nruth633/3-wheel-balancing-robot/firmware_main/Docs_Process/Acrylic_base_drawing.png

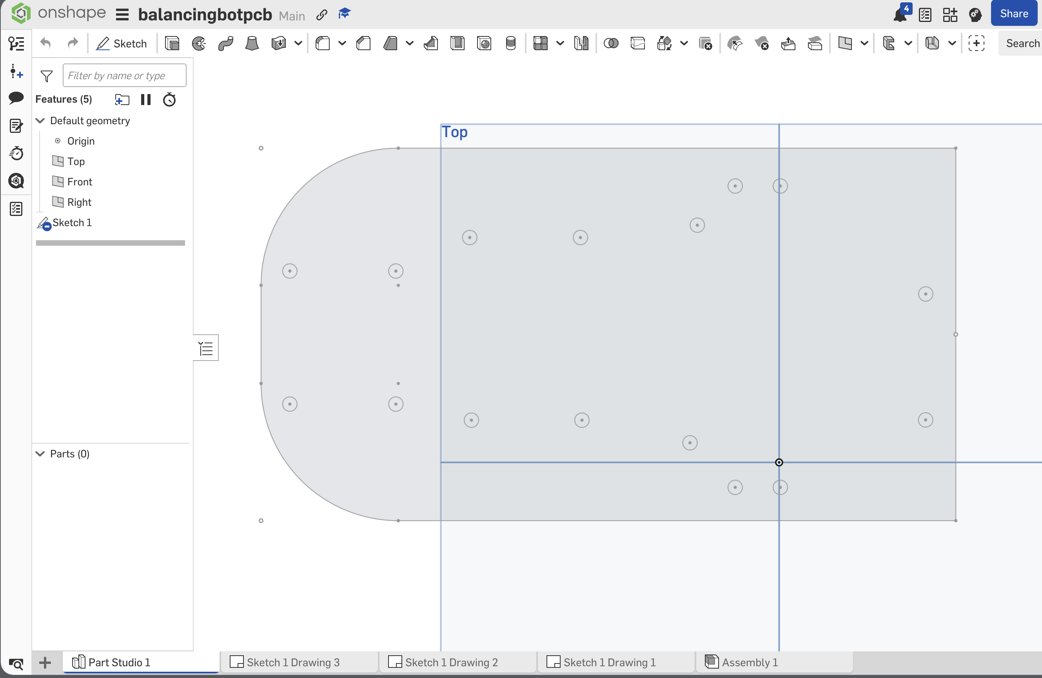
firmware_main/Docs_Process/Acrylic_base_drawing.png
