nruth633/3-wheel-balancing-robot/firmware_main/Components/MPU6050/imu_dimensions.jpg

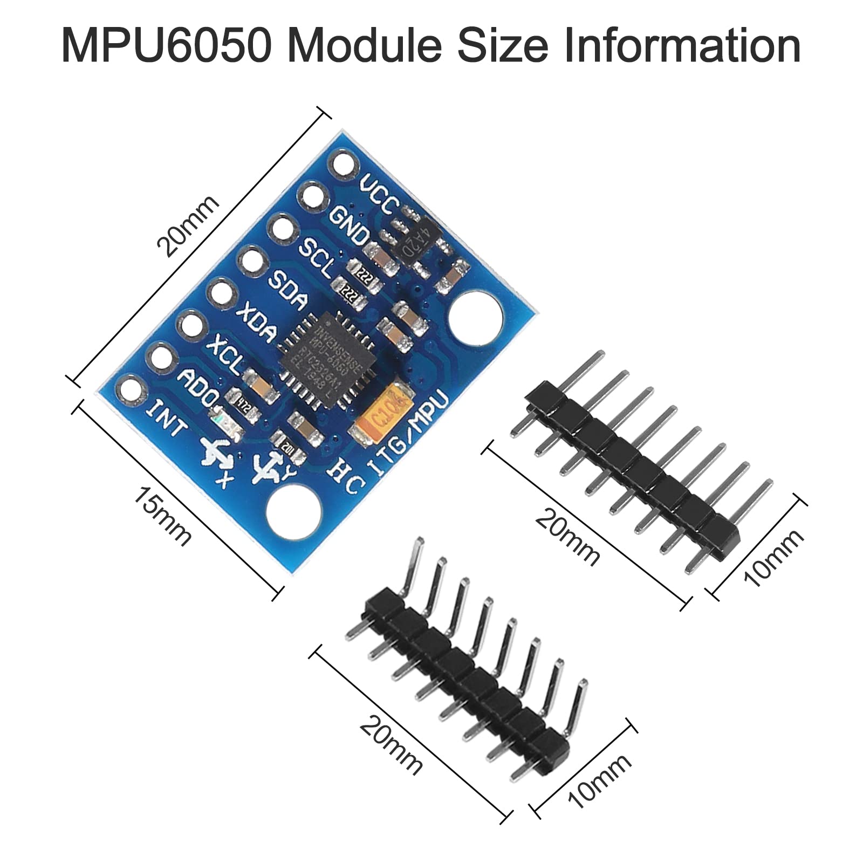
firmware_main/Components/MPU6050/imu_dimensions.jpg
