nruth633/3-wheel-balancing-robot/firmware_main/Docs_Process/PCB_measurements.png

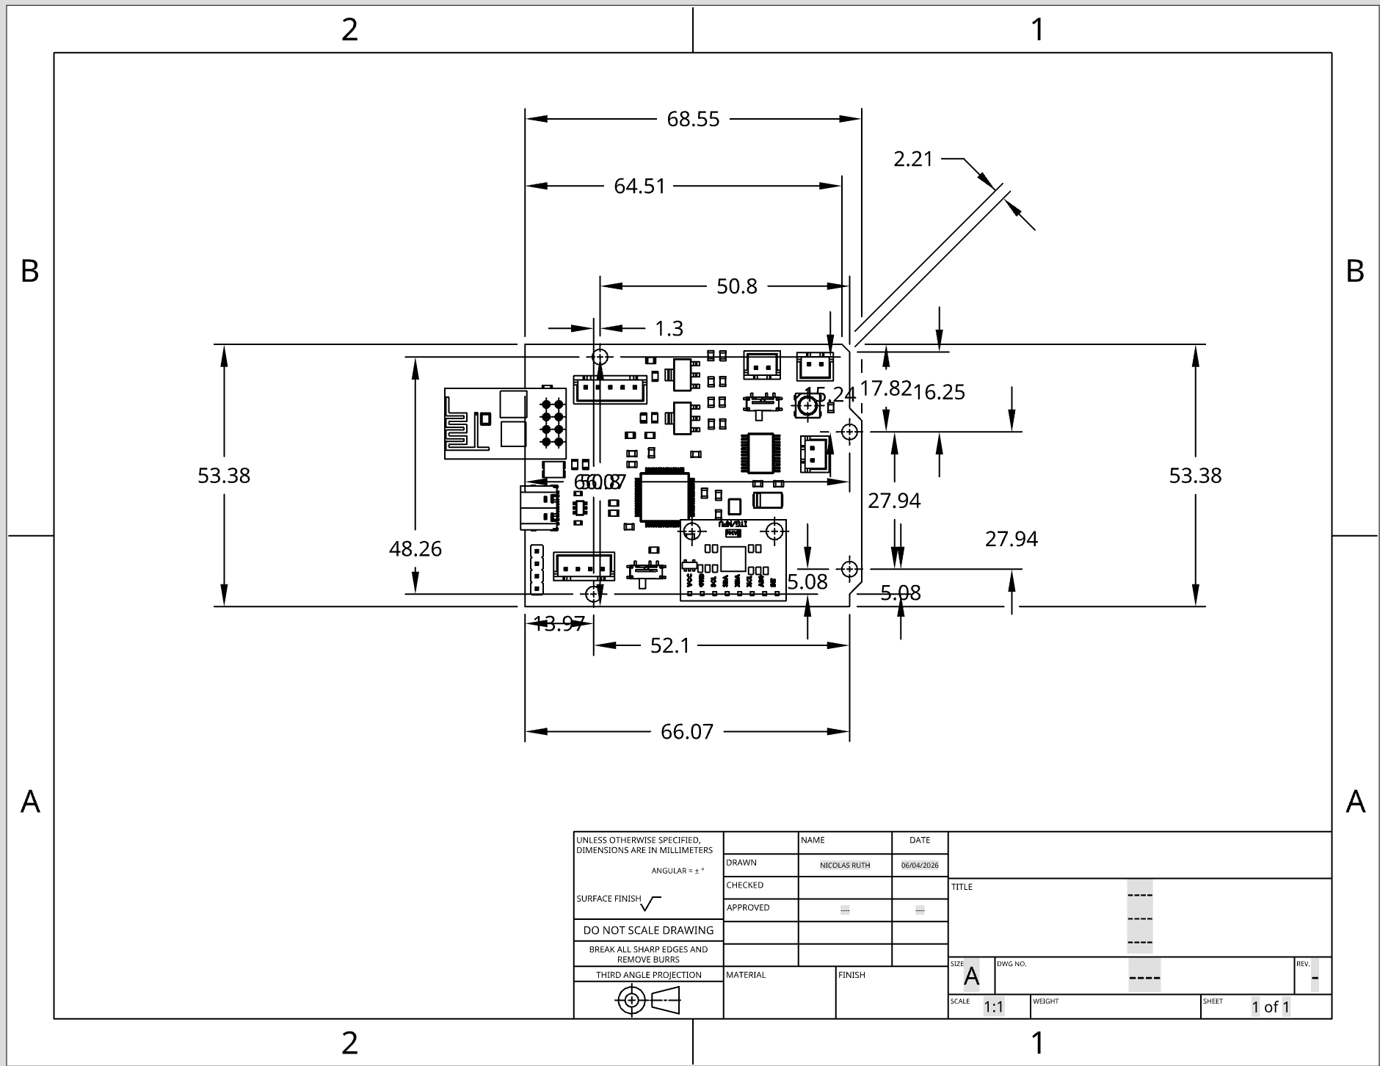
firmware_main/Docs_Process/PCB_measurements.png
