nruth633/3-wheel-balancing-robot/pcb/docs/I messed up the footprints but I will fix.png

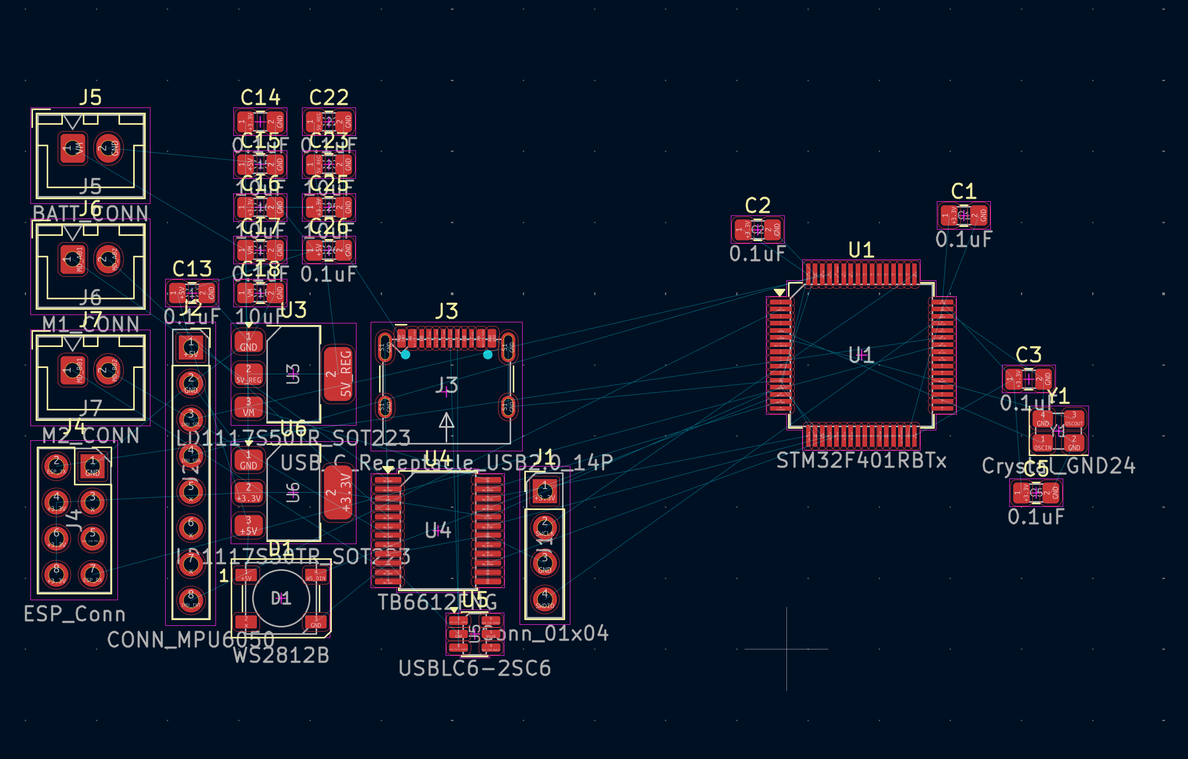
pcb/docs/I messed up the footprints but I will fix.png
